mikeysklar/sdio-shim/kicad/sdio-shim.kicad_sch

## KiCad design kicad/sdio-shim.kicad_sch (2026-07-09)

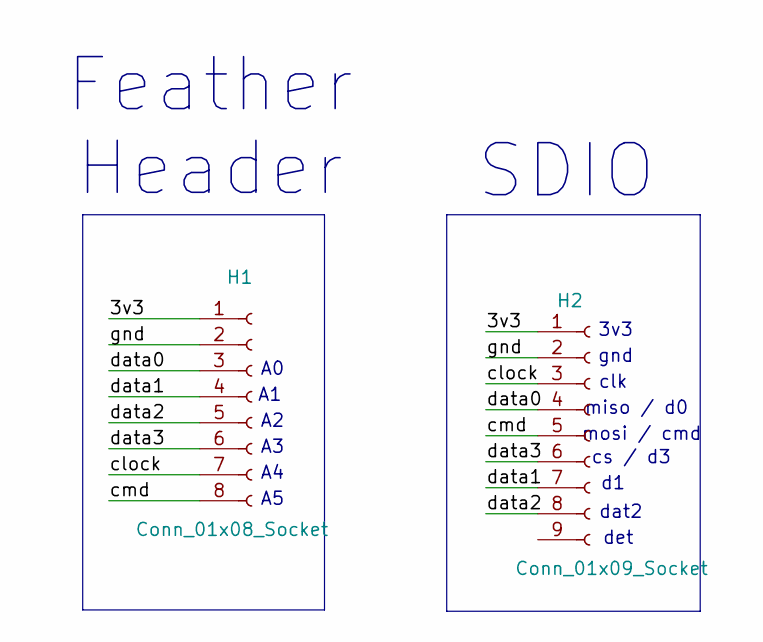
[picture p7: schematic sdio-shim.kicad_sch]

Parts:
H1: Conn_01x08_Socket; header-rt-ang-smd
H2: Conn_01x09_Socket; 2x09-adafruit-smt-featherwing-4743

Connections:
3v3: H1.1, H2.1
clock: H1.7, H2.3
cmd: H1.8, H2.5
data0: H1.3, H2.4
data1: H1.4, H2.7
data2: H1.5, H2.8
data3: H1.6, H2.6
gnd: H1.2, H2.2

Notes on the sheet:
miso / d0
dat2
gnd
cs / d3
mosi / cmd
3v3
det
SDIO
Feather Header
clk
